Alan-JH/PCB-Heater/Firmware/Firmware/SegmentMap.h

/* Digits:
 * 1 2 3 | 4 5 6
 * 7 8 9
 * 
 * Segments:
 *  --0--
 * |     |
 * |     |
 * 5     1
 * |     |
 * |     |
 *  --6--
 * |     |
 * |     |
 * 4     2
 * |     |
 * |     |
 *  --3--
 */

 uint8_t segDigMap[9][7][2] = {
  {{0,  0b00001000}, {0,  0b00010000}, {0,  0b00100000}, {0,  0b00000001}, {0,  0b00000010}, {0,  0b00000100}, {0,  0b01000000}},
  {{1,  0b00001000}, {1,  0b00010000}, {1,  0b00100000}, {1,  0b00000001}, {1,  0b00000010}, {1,  0b00000100}, {1,  0b01000000}},
  {{2,  0b00001000}, {2,  0b00010000}, {2,  0b00100000}, {2,  0b00000001}, {2,  0b00000010}, {2,  0b00000100}, {2,  0b01000000}},
  {{8,  0b00000100}, {8,  0b00001000}, {8,  0b00010000}, {0,  0b10000000}, {8,  0b00000001}, {8,  0b00000010}, {8,  0b00100000}},
  {{9,  0b00000100}, {9,  0b00001000}, {9,  0b00010000}, {1,  0b10000000}, {9,  0b00000001}, {9,  0b00000010}, {9,  0b00100000}},
  {{10, 0b00000100}, {10, 0b00001000}, {10, 0b00010000}, {2,  0b10000000}, {10, 0b00000001}, {10, 0b00000010}, {10, 0b00100000}},
  {{5,  0b00001000}, {5,  0b00010000}, {5,  0b00100000}, {5,  0b00000001}, {5,  0b00000010}, {5,  0b00000100}, {5,  0b01000000}},
  {{4,  0b00001000}, {4,  0b00010000}, {4,  0b00100000}, {4,  0b00000001}, {4,  0b00000010}, {4,  0b00000100}, {4,  0b01000000}},
  {{3,  0b00001000}, {3,  0b00010000}, {3,  0b00100000}, {3,  0b00000001}, {3,  0b00000010}, {3,  0b00000100}, {3,  0b01000000}}
 };

 bool charMap[10][7] = {
  {1, 1, 1, 1, 1, 1, 0},
  {0, 1, 1, 0, 0, 0, 0},
  {1, 1, 0, 1, 1, 0, 1},
  {1, 1, 1, 1, 0, 0, 1},
  {0, 1, 1, 0, 0, 1, 1},
  {1, 0, 1, 1, 0, 1, 1},
  {0, 0, 1, 1, 1, 1, 1},
  {1, 1, 1, 0, 0, 0, 0},
  {1, 1, 1, 1, 1, 1, 1},
  {1, 1, 1, 0, 0, 1, 1}
 };
